raphaelbs/Plug.ar/Estágio 1/Fotos/Conteiner - 2a versao.PNG

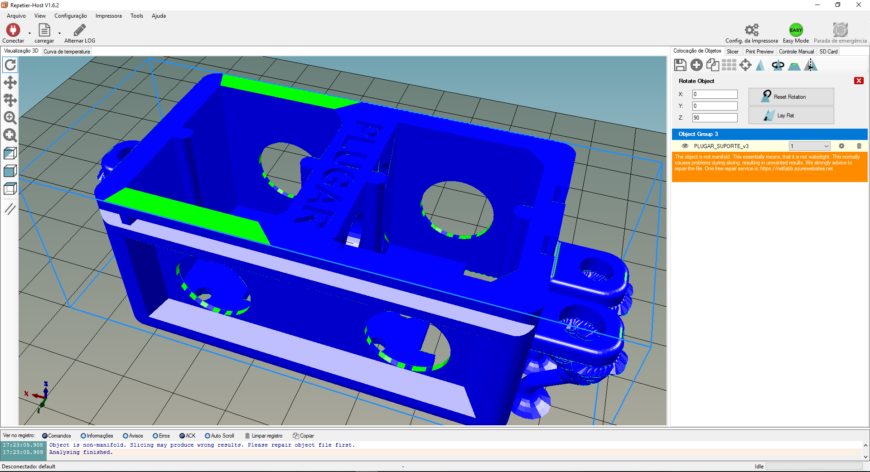
Estágio 1/Fotos/Conteiner - 2a versao.PNG
