raphaelbs/Plug.ar/Estágio 1/Fotos/Conteiner - pinagem traseira.PNG

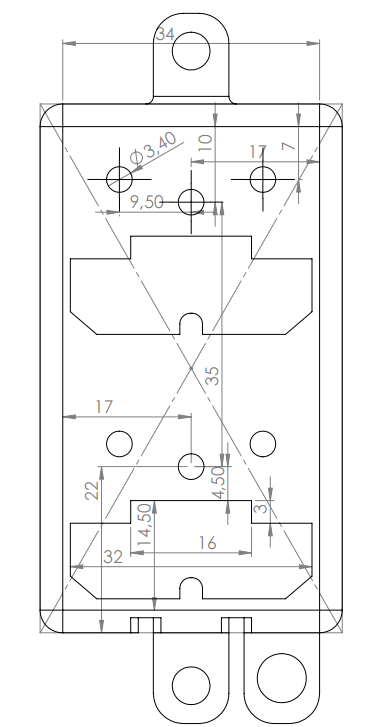
Estágio 1/Fotos/Conteiner - pinagem traseira.PNG
