raphaelbs/Plug.ar/Estágio 1/Fotos/Contêiner.PNG

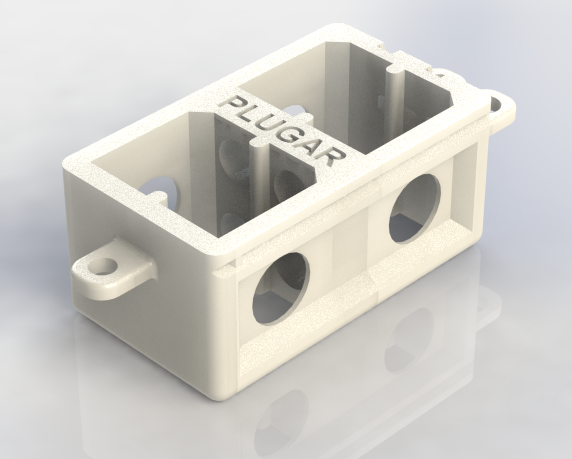
Estágio 1/Fotos/Contêiner.PNG
