raphaelbs/Plug.ar/Estágio 1/Fotos/Eagle Lib - MODULOPAD - package.PNG

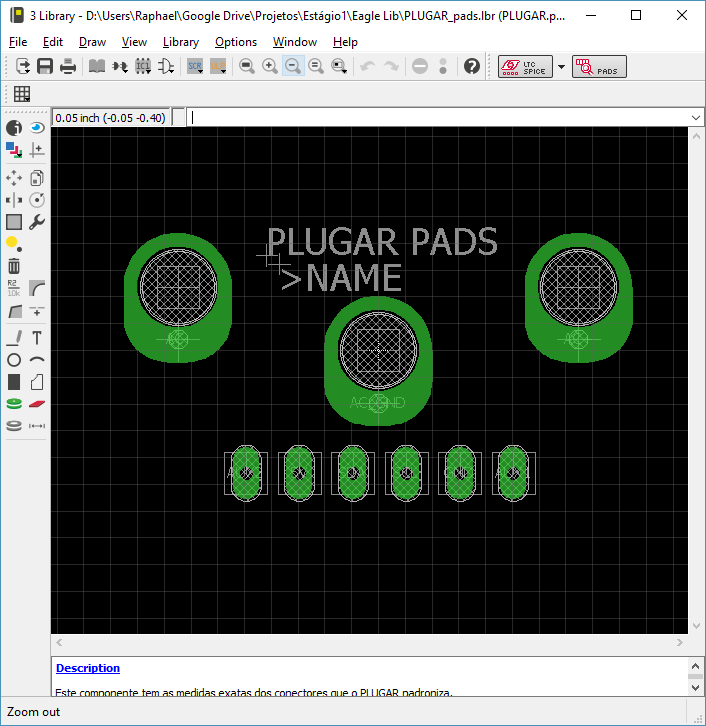
Estágio 1/Fotos/Eagle Lib - MODULOPAD - package.PNG
