raphaelbs/Plug.ar/Estágio 1/Fotos/Eagle Lib - MODULOPAD.PNG

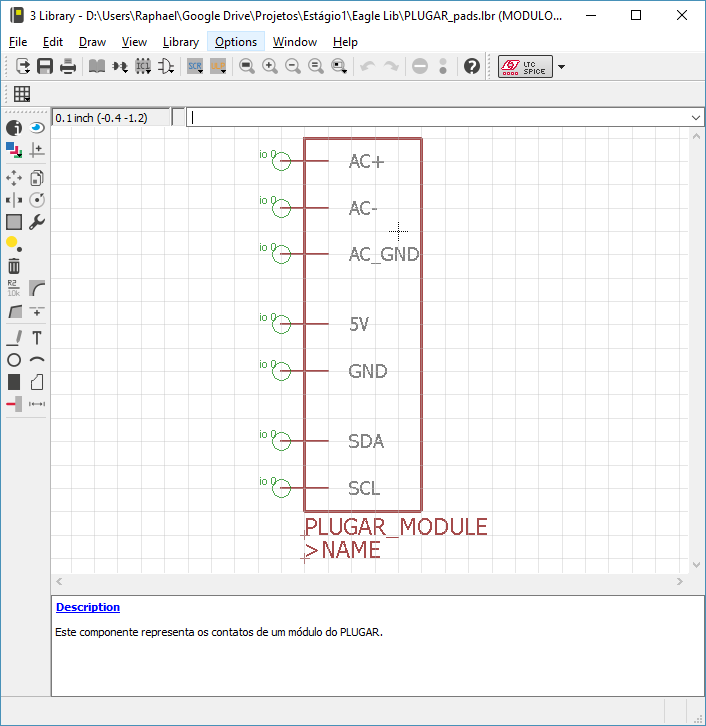
Estágio 1/Fotos/Eagle Lib - MODULOPAD.PNG
