raphaelbs/Plug.ar/Estágio 1/Fotos/Fixação - Tampa conteiner.jpeg

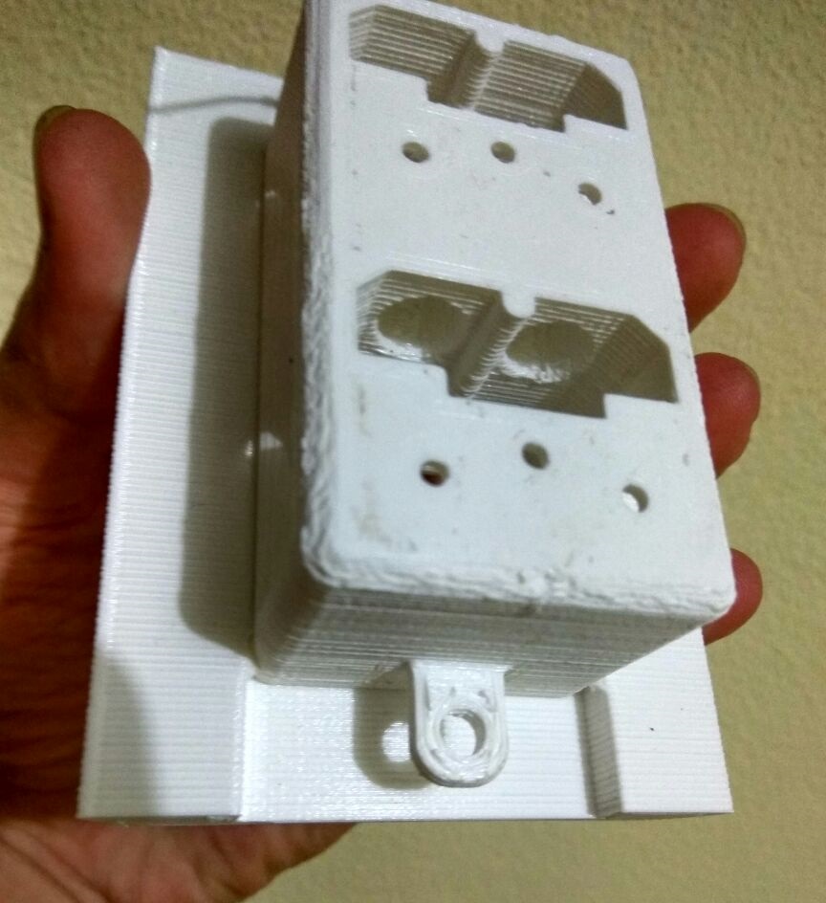
Estágio 1/Fotos/Fixação - Tampa conteiner.jpeg
