raphaelbs/Plug.ar/Estágio 1/Fotos/pinos parafusaveis.jpg

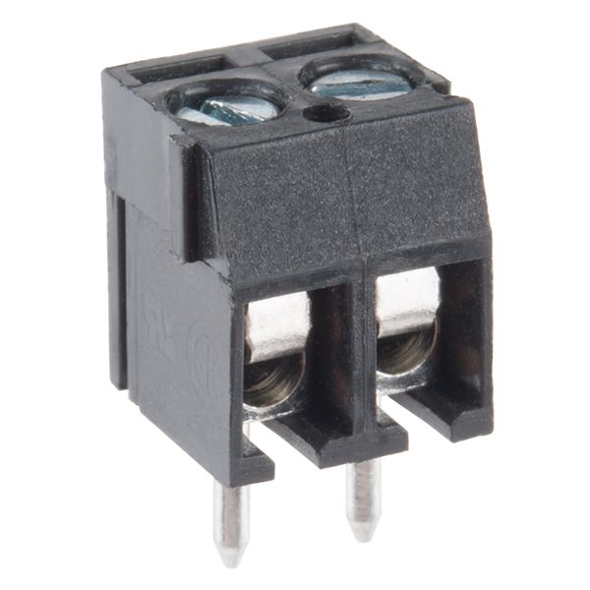
Estágio 1/Fotos/pinos parafusaveis.jpg
