raphaelbs/Plug.ar/Estágio 1/Fotos/Tampa.PNG

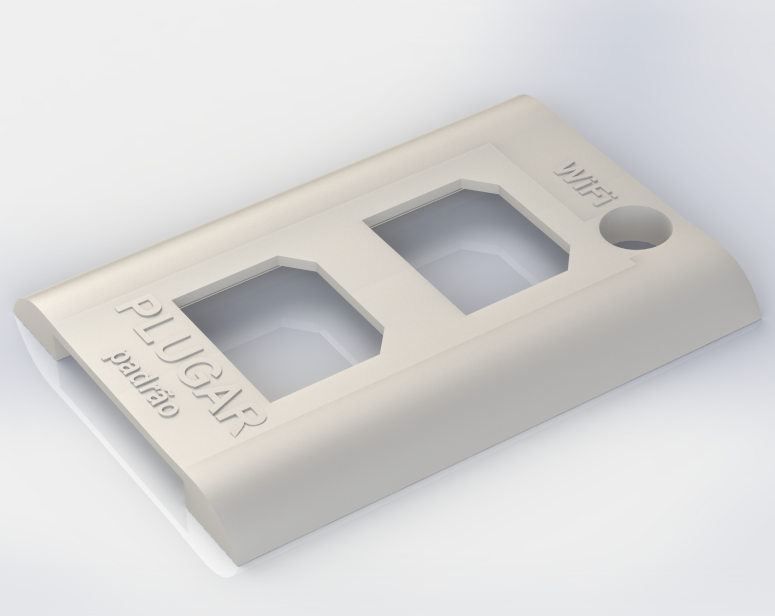
Estágio 1/Fotos/Tampa.PNG
