raphaelbs/Plug.ar/Estágio 2/Fotos/ciclone_pcb.frezando.jpeg

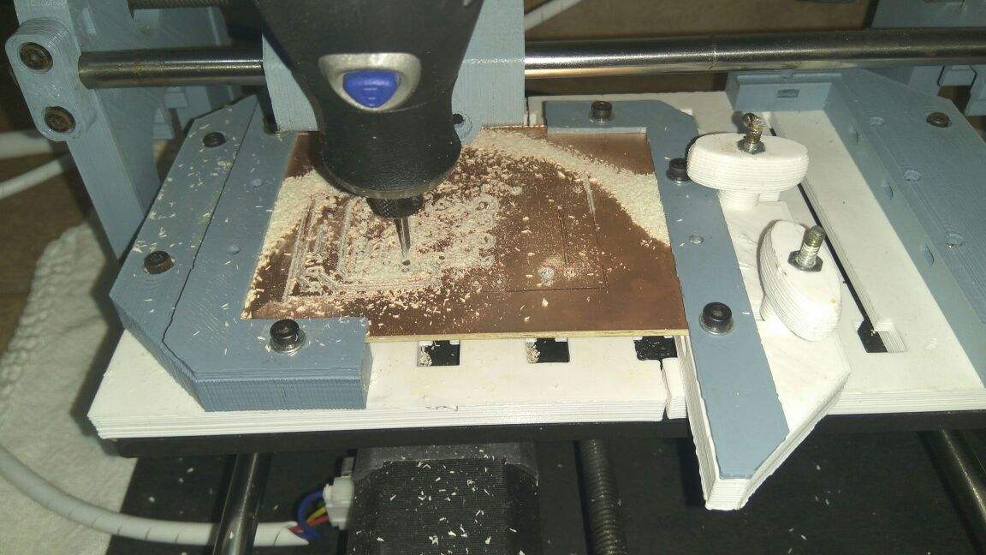
Estágio 2/Fotos/ciclone_pcb.frezando.jpeg
