raphaelbs/Plug.ar/Estágio 2/Fotos/cicuito.principal.montado.jpeg

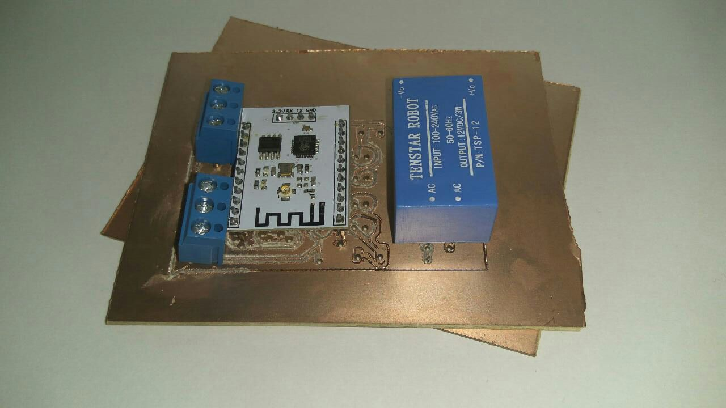
Estágio 2/Fotos/cicuito.principal.montado.jpeg
