raphaelbs/Plug.ar/Estágio 2/Fotos/circuito_principal.v2.jpeg

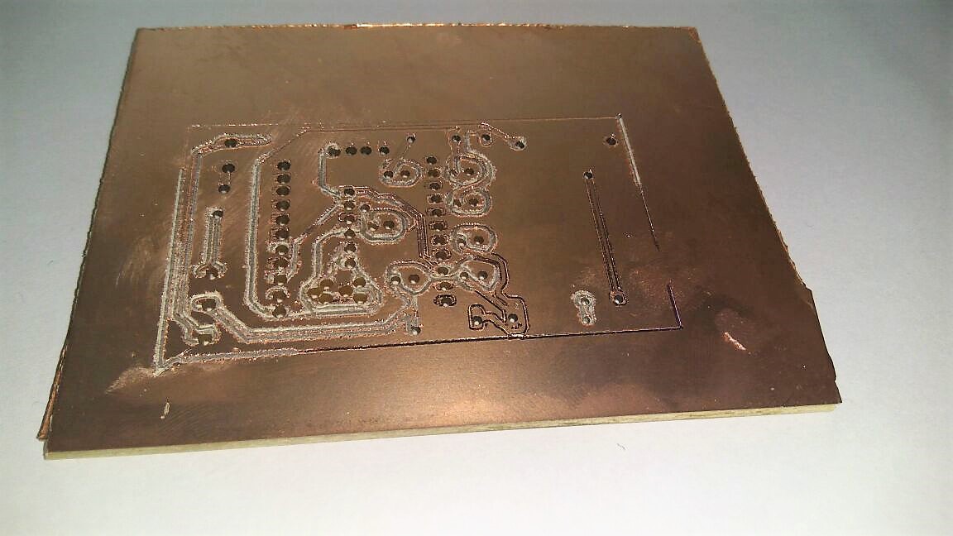
Estágio 2/Fotos/circuito_principal.v2.jpeg
