raphaelbs/Plug.ar/Estágio 2/Fotos/codigos_gcode.png

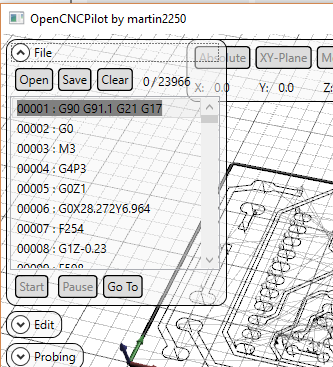
Estágio 2/Fotos/codigos_gcode.png
