raphaelbs/Plug.ar/Estágio 2/Fotos/Conteiner - versao reduzida.PNG

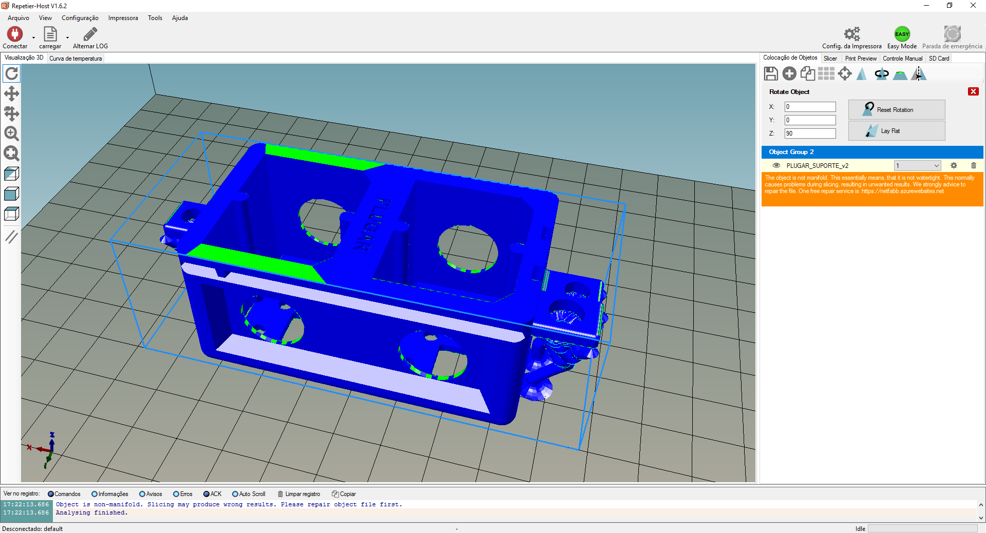
Estágio 2/Fotos/Conteiner - versao reduzida.PNG
