raphaelbs/Plug.ar/Estágio 2/Fotos/contêiner.v4.costas.JPG

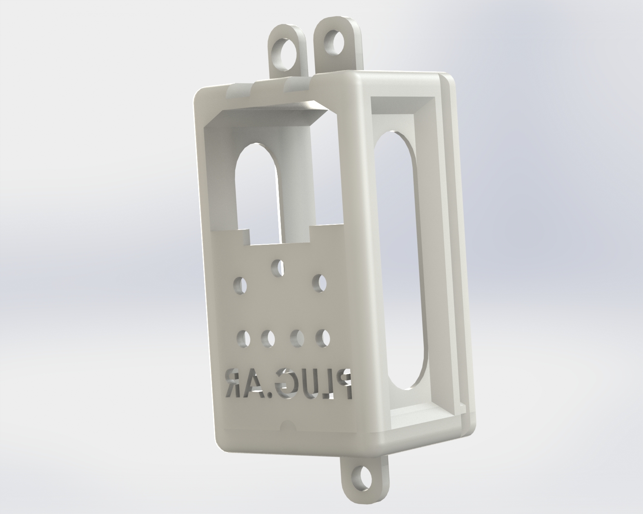
Estágio 2/Fotos/contêiner.v4.costas.JPG
