raphaelbs/Plug.ar/Estágio 2/Fotos/contêiner.v4.frontal.JPG

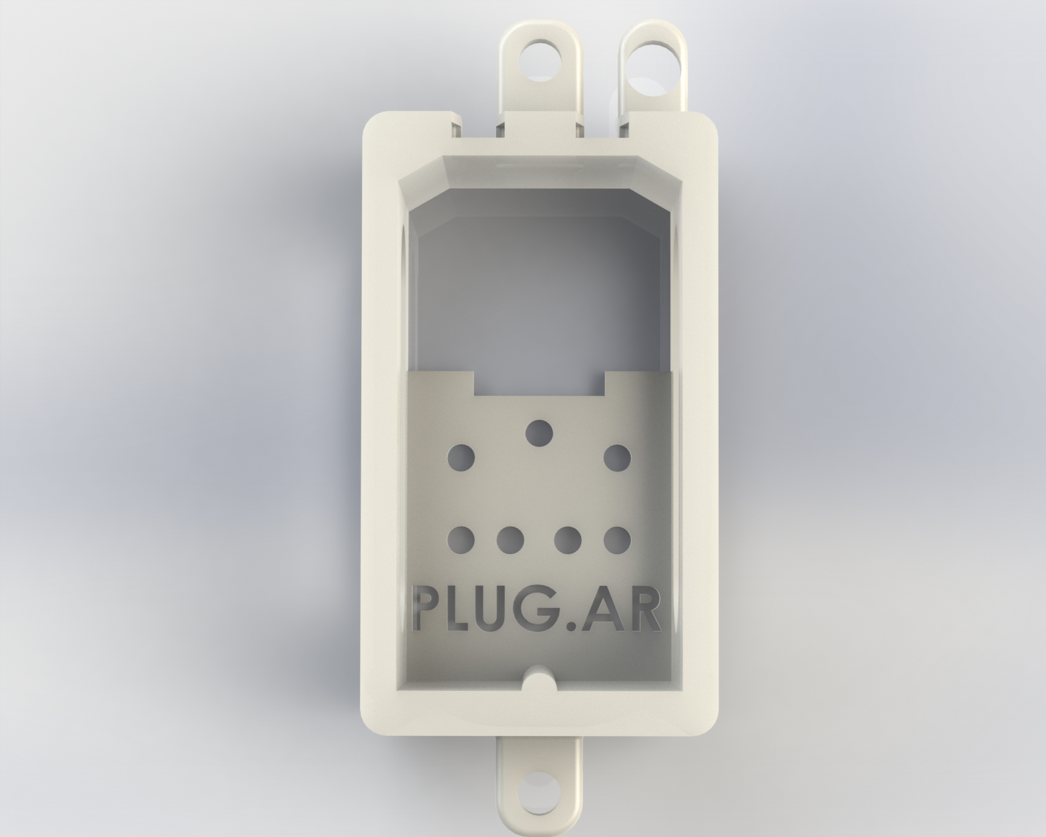
Estágio 2/Fotos/contêiner.v4.frontal.JPG
