raphaelbs/Plug.ar/Estágio 2/Fotos/contêiner.v4.i3d.lateral.jpeg

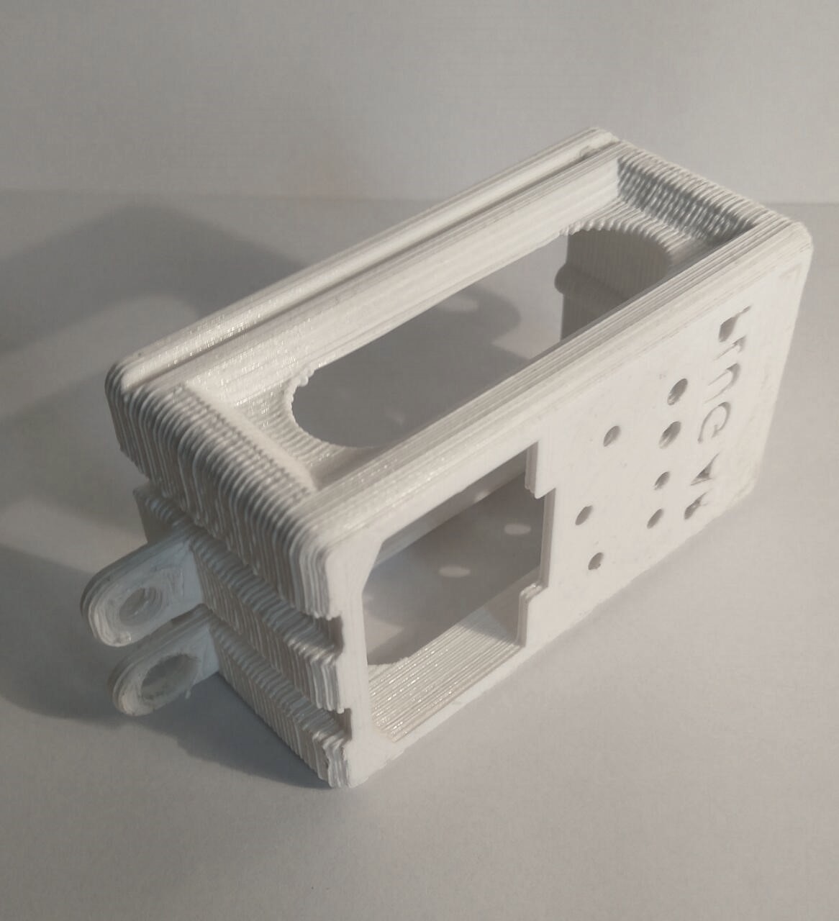
Estágio 2/Fotos/contêiner.v4.i3d.lateral.jpeg
