raphaelbs/Plug.ar/Estágio 2/Fotos/Eagle Lib - ESP201 - package.PNG

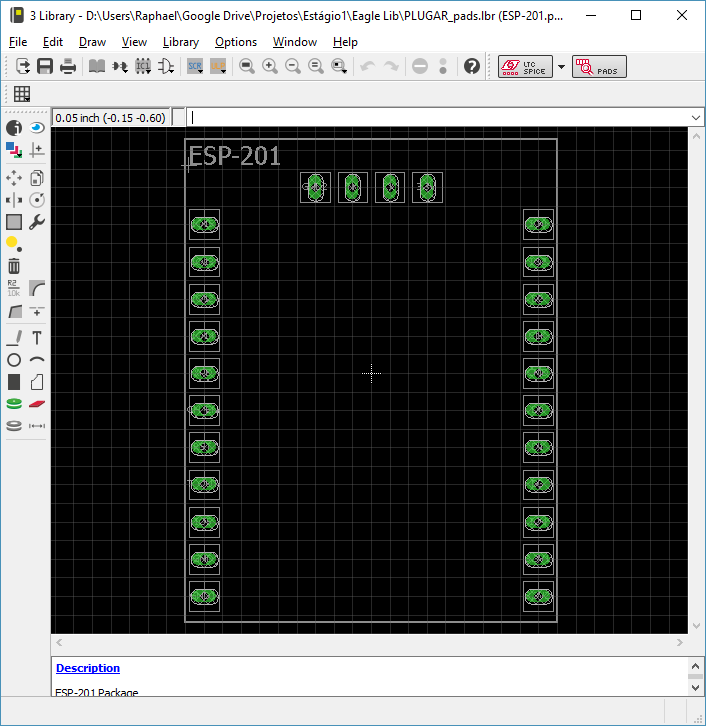
Estágio 2/Fotos/Eagle Lib - ESP201 - package.PNG
