raphaelbs/Plug.ar/Estágio 2/Fotos/Eagle Lib - ESP201.PNG

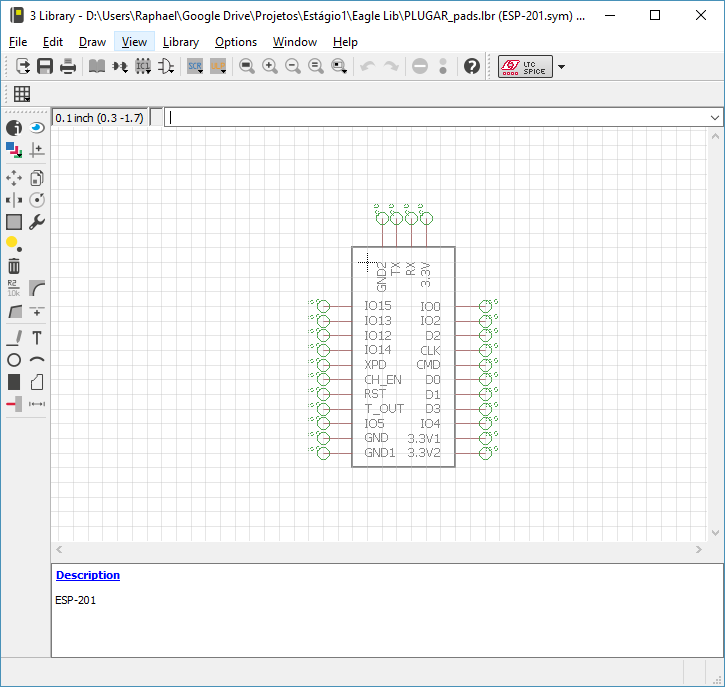
Estágio 2/Fotos/Eagle Lib - ESP201.PNG
