raphaelbs/Plug.ar/Estágio 2/Fotos/Eagle Lib.PNG

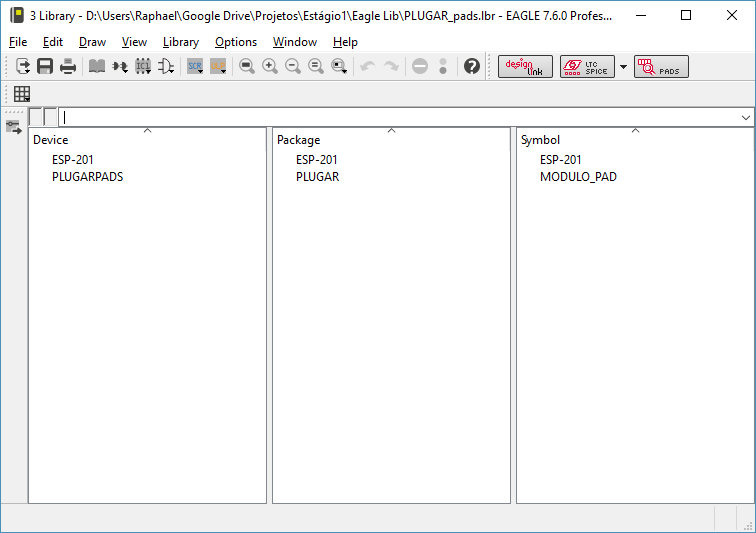
Estágio 2/Fotos/Eagle Lib.PNG
