raphaelbs/Plug.ar/Estágio 2/Fotos/esp201_antena.jpeg

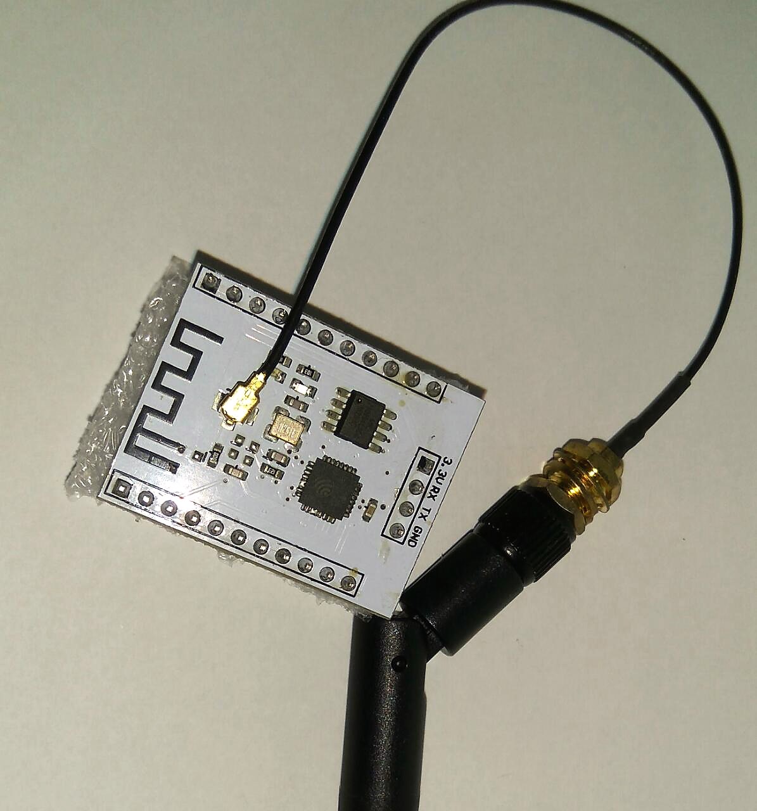
Estágio 2/Fotos/esp201_antena.jpeg
