raphaelbs/Plug.ar/Estágio 2/Fotos/módulo-base.v2.costas.JPG

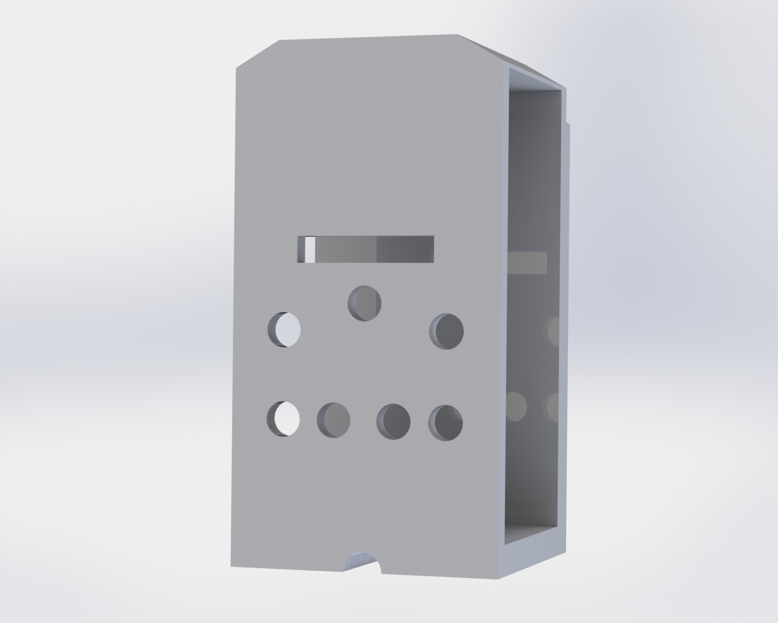
Estágio 2/Fotos/módulo-base.v2.costas.JPG
