raphaelbs/Plug.ar/Estágio 2/Fotos/pcf8574.jpeg

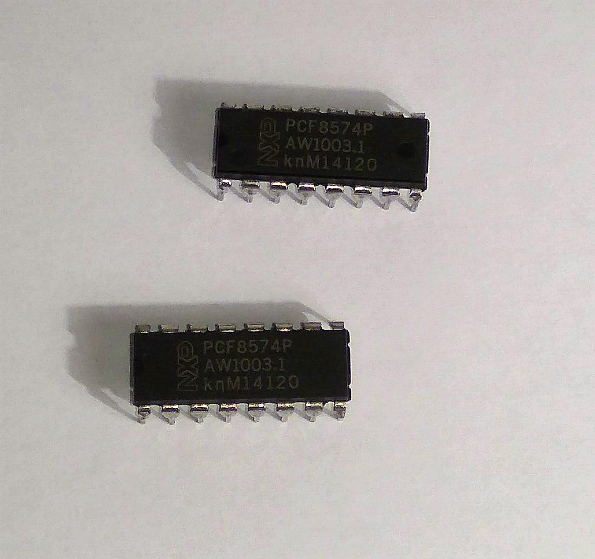
Estágio 2/Fotos/pcf8574.jpeg
