raphaelbs/Plug.ar/Estágio 2/Fotos/Placa principal - Esquemática.PNG.png

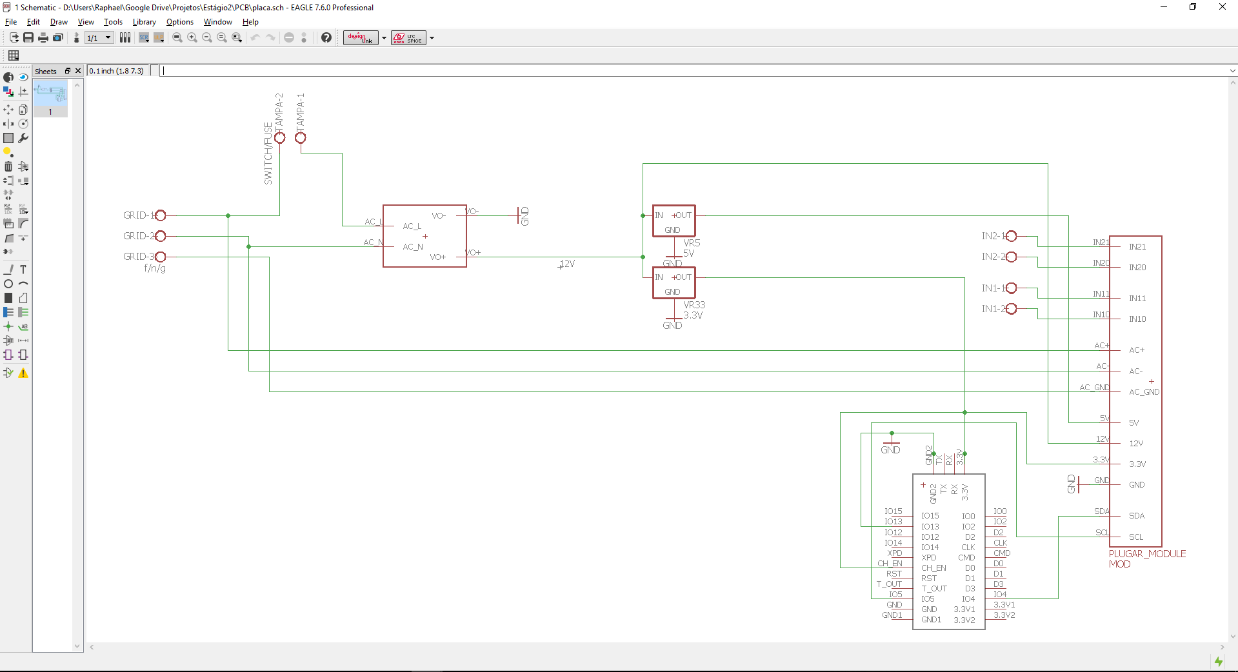
Estágio 2/Fotos/Placa principal - Esquemática.PNG.png
