raphaelbs/Plug.ar/Estágio 2/Fotos/Placa principal.PNG

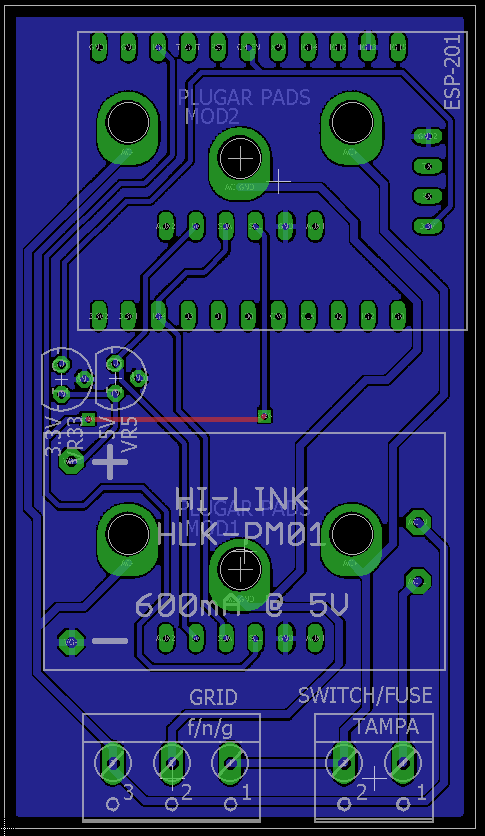
Estágio 2/Fotos/Placa principal.PNG
