raphaelbs/Plug.ar/Estágio 2/Fotos/Placa principal.PNG.png

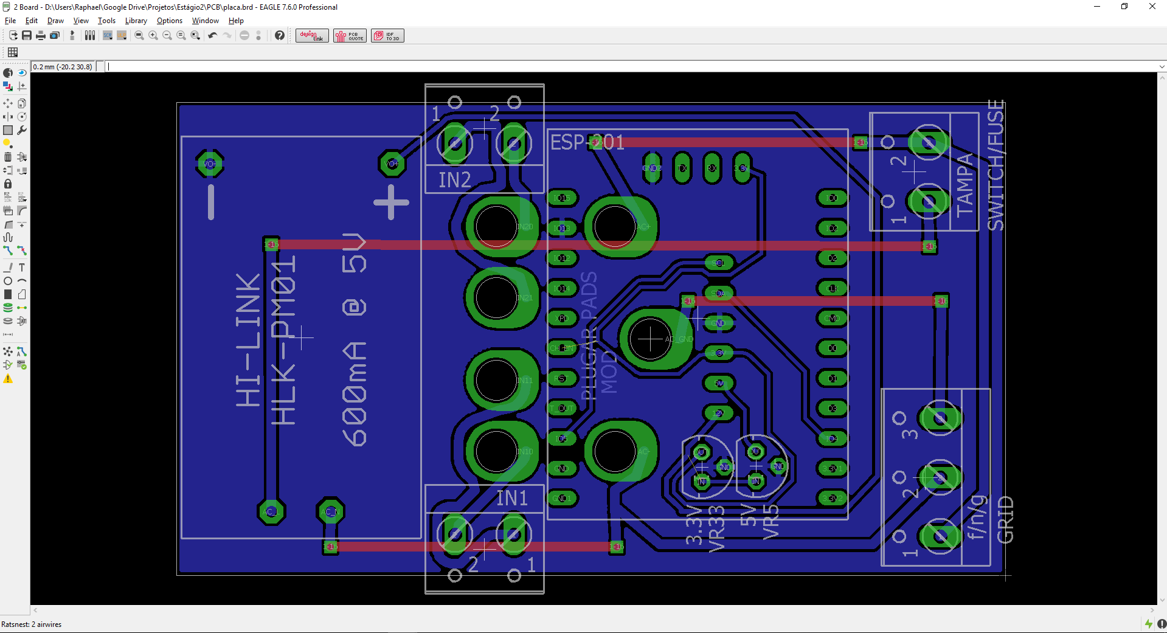
Estágio 2/Fotos/Placa principal.PNG.png
