raphaelbs/Plug.ar/Estágio 2/Fotos/PLUGAR.jpeg

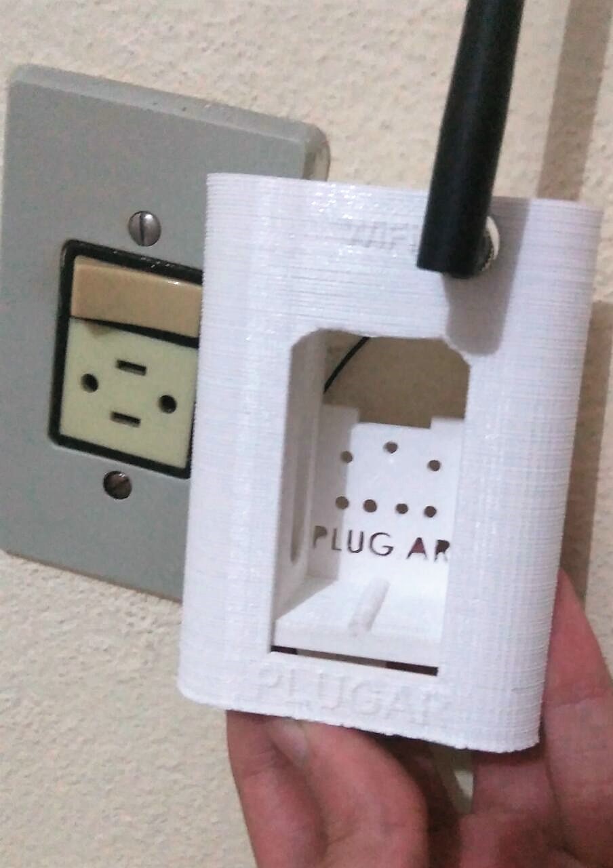
Estágio 2/Fotos/PLUGAR.jpeg
