raphaelbs/Plug.ar/Estágio 2/Fotos/PLUGAR.PNG

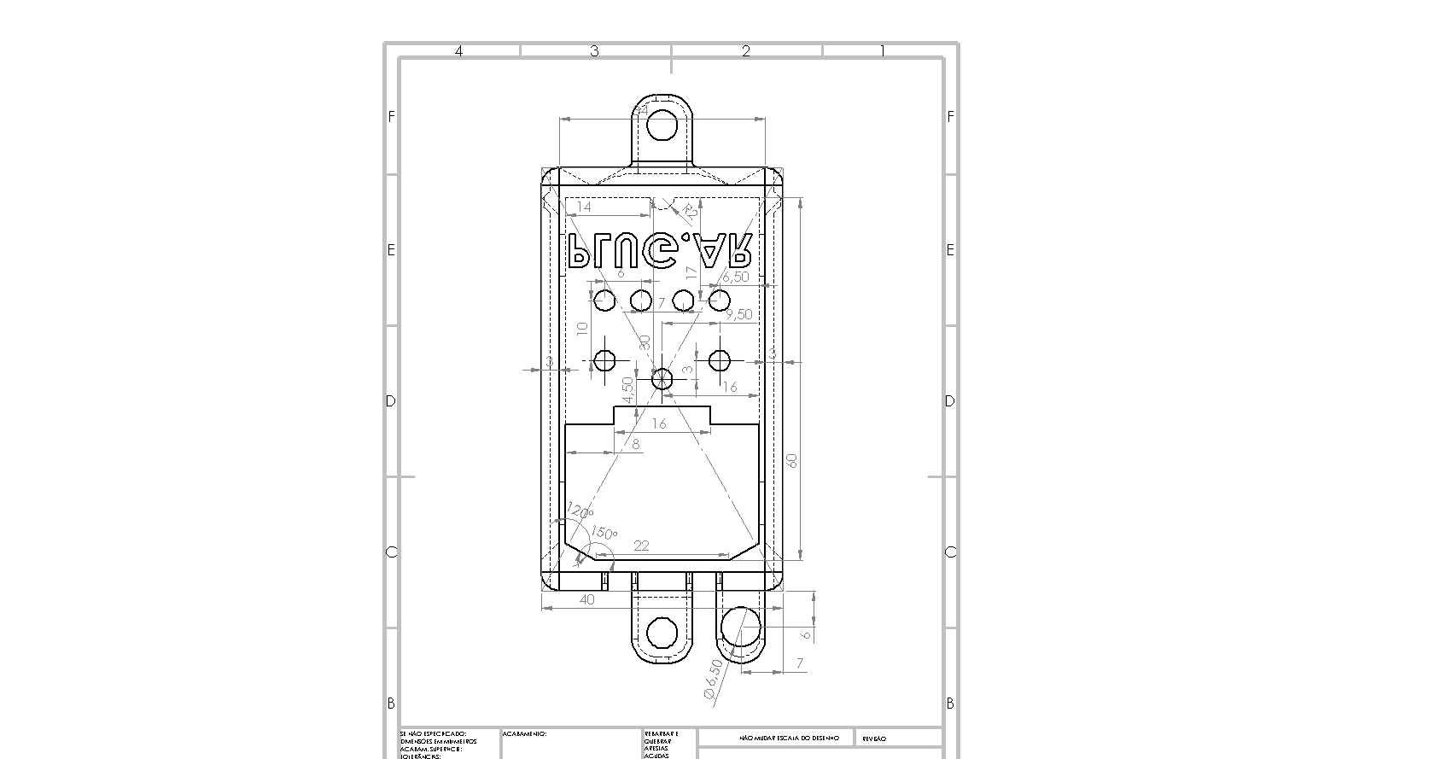
Estágio 2/Fotos/PLUGAR.PNG
