raphaelbs/Plug.ar/Estágio 2/Fotos/tampa.v3.costas.JPG

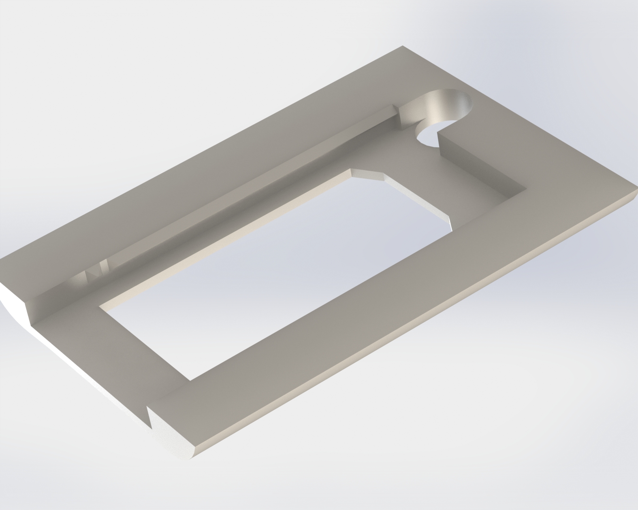
Estágio 2/Fotos/tampa.v3.costas.JPG
