raphaelbs/Plug.ar/Estágio 2/Fotos/tampa.v3.i3d.comparativo_tomada.jpeg

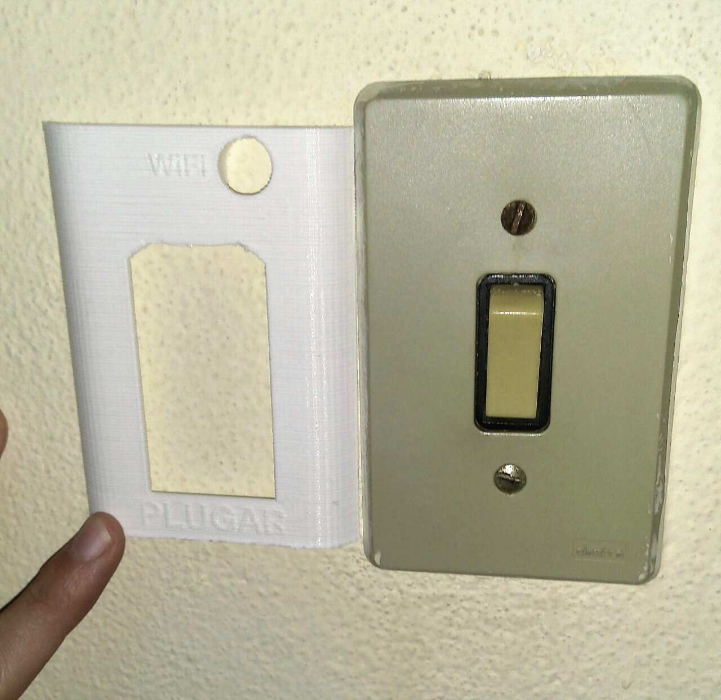
Estágio 2/Fotos/tampa.v3.i3d.comparativo_tomada.jpeg
