raphaelbs/Plug.ar/Estágio 2/Fotos/tampa.v3.i3d.ortogonal.jpeg

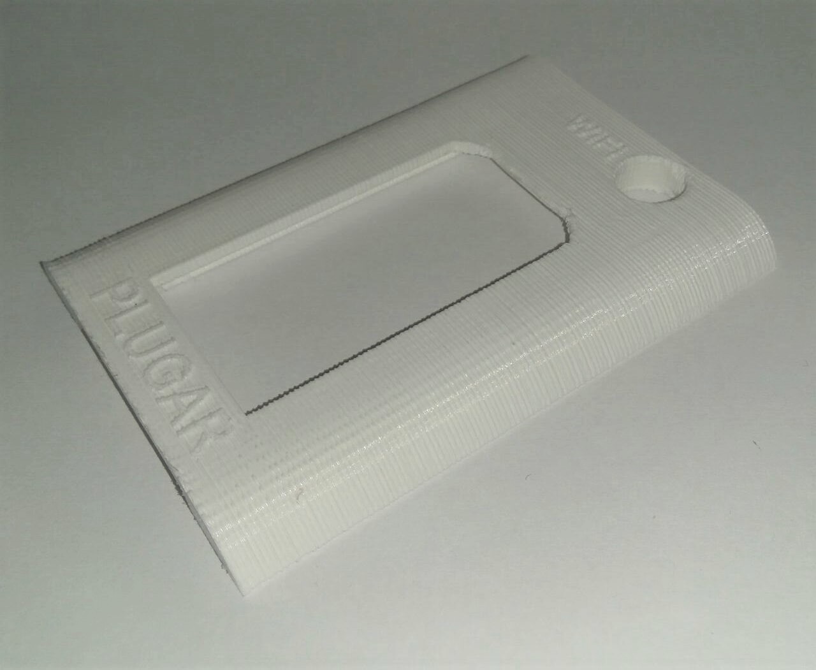
Estágio 2/Fotos/tampa.v3.i3d.ortogonal.jpeg
