raphaelbs/Plug.ar/Estágio 1/Fotos/Montagem com tampa.PNG

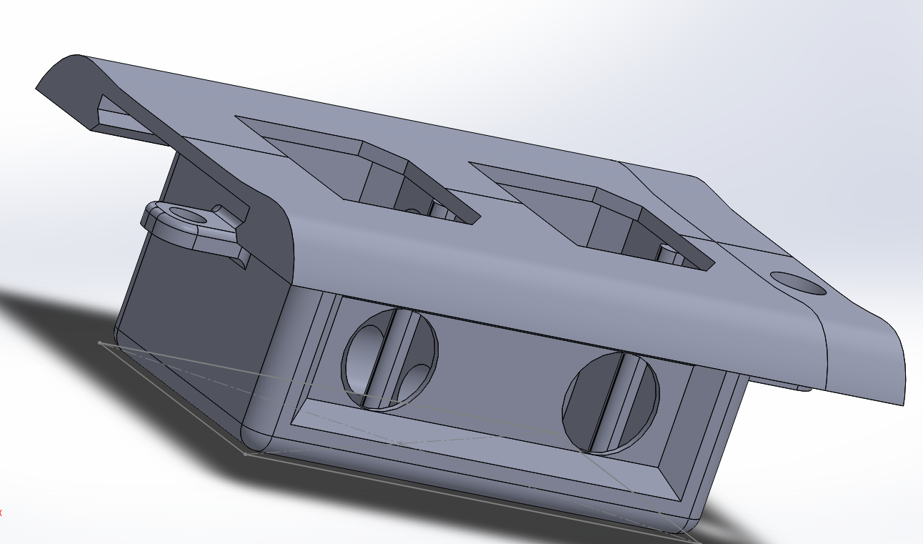
Estágio 1/Fotos/Montagem com tampa.PNG
