raphaelbs/Plug.ar/Estágio 2/Fotos/montagem.i3d.costas.jpeg

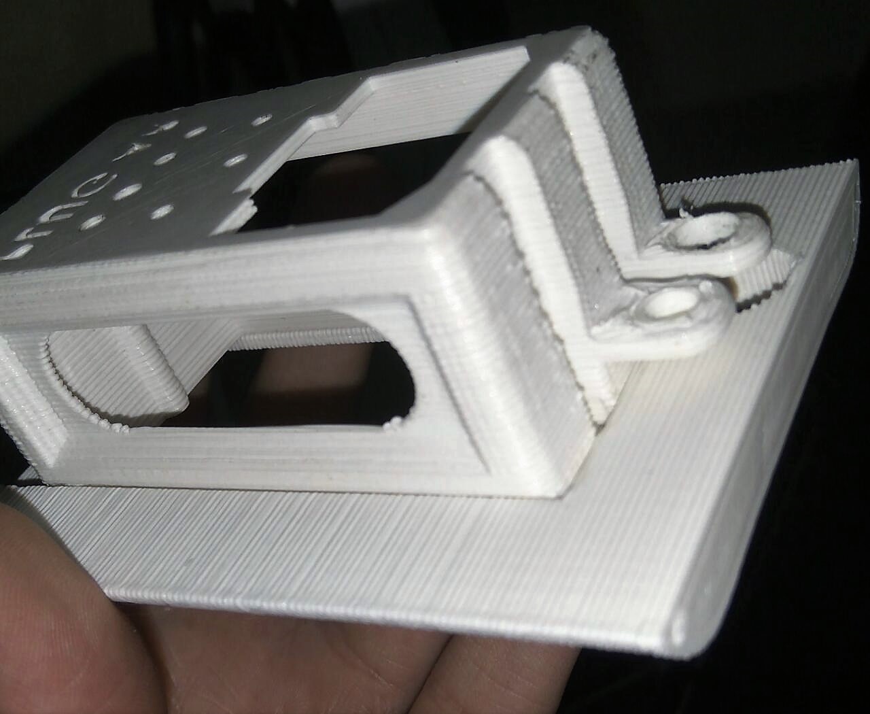
Estágio 2/Fotos/montagem.i3d.costas.jpeg
