raphaelbs/Plug.ar/Estágio 2/Fotos/montagem.i3d.frontal.encaixe_modulo.jpeg

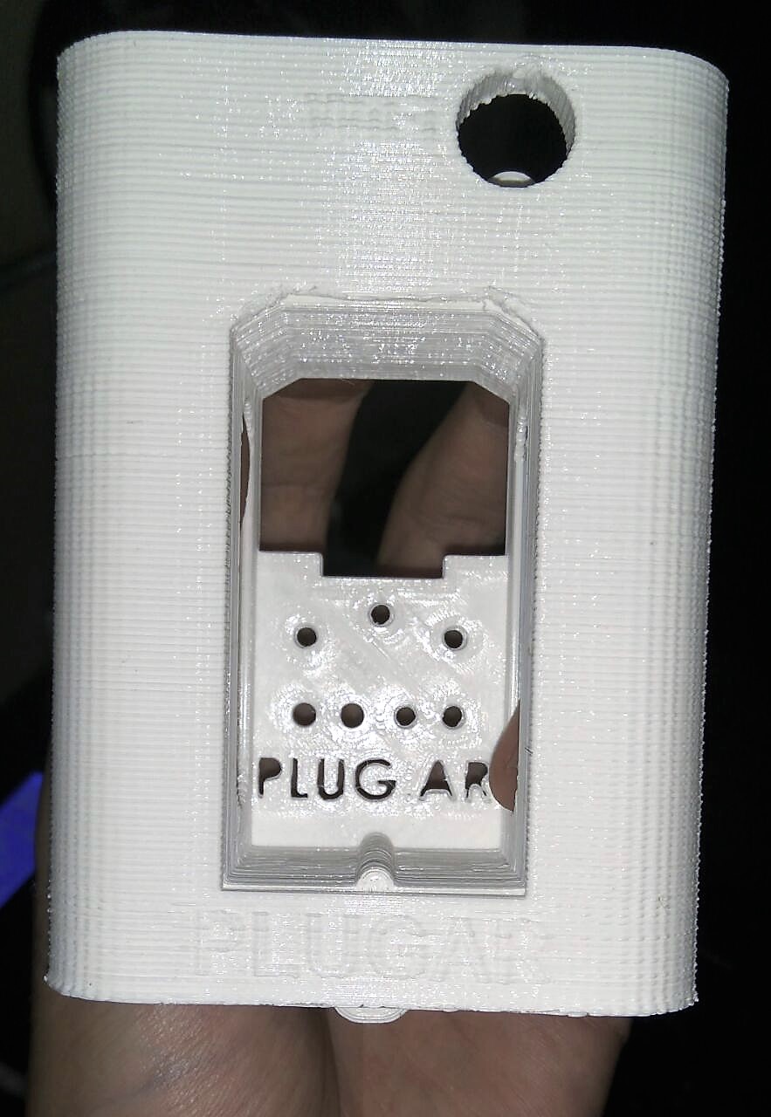
Estágio 2/Fotos/montagem.i3d.frontal.encaixe_modulo.jpeg
