raphaelbs/Plug.ar/Estágio 2/Fotos/opencncpilot.calibrando.jpeg

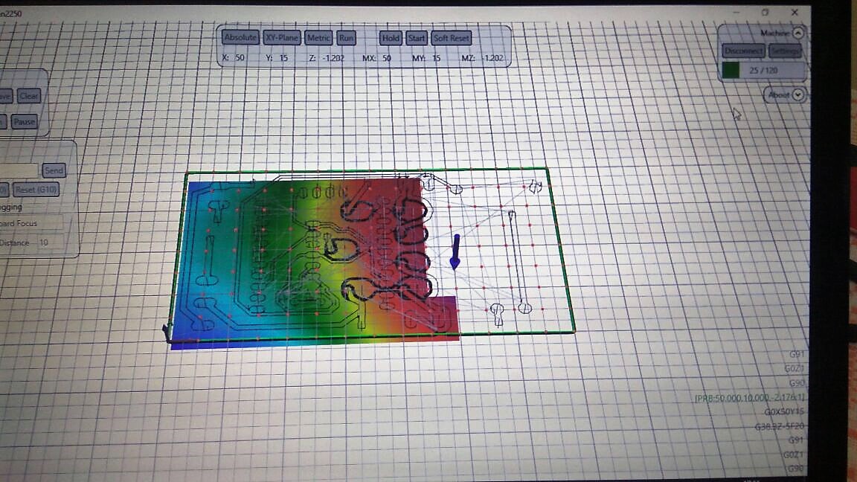
Estágio 2/Fotos/opencncpilot.calibrando.jpeg
